maltaisn/game-console/sw/app/system/include/comm.h

/*
 * Copyright 2021 Nicolas Maltais
 *
 * Licensed under the Apache License, Version 2.0 (the "License");
 * you may not use this file except in compliance with the License.
 * You may obtain a copy of the License at
 *
 *     http://www.apache.org/licenses/LICENSE-2.0
 *
 * Unless required by applicable law or agreed to in writing, software
 * distributed under the License is distributed on an "AS IS" BASIS,
 * WITHOUT WARRANTIES OR CONDITIONS OF ANY KIND, either express or implied.
 * See the License for the specific language governing permissions and
 * limitations under the License.
 */

#ifndef SYSTEM_COMM_H
#define SYSTEM_COMM_H

#include <stdint.h>

#define PACKET_SIGNATURE 0x73
#define PACKET_MAX_SIZE 256
#define PACKET_HEADER_SIZE 3
#define PAYLOAD_MAX_SIZE (PACKET_MAX_SIZE - PACKET_HEADER_SIZE)

/*
 * This module defines an interface for communicating to the game console via the UART link.
 * There are a few packets defined for interating with the console.
 * Each packet transmitted and received has the following format:
 *
 * [0]: signature byte 0xc3
 * [1]: packet type
 * [2]: total packet length (=n), -1 (2-255)
 * [3..n]: payload
 *
 * The payload of different packet types defined are described below.
 * "RX" refers to the receiving side of the game console and "TX" refers to the transmitting side.
 *
 * For every packet sent, the transmitter should wait until the response packet is fully received.
 * The reason for this is that the RX buffer size is limited to the size of one packet.
 */

typedef enum {
    /**
     * Get version info
     * - RX payload: empty
     * - TX payload:
     * [0..1]: system app version
     * [2..3]: bootloader version
     * [4..5]: gcprog first compatible version
     */
    PACKET_VERSION = 0x00,

    /**
     * Transfer data on the SPI bus
     * RX & TX packets have an identical format.
     * [0]: bits [0:1] indicate the selected peripheral
     *      - 0x0: flash memory
     *      - 0x1: EEPROM memory
     *      - 0x2: OLED display
     *      - 0x3: reserved
     *      bit [7] is 1 if this is the last transfer, which means the CS line will be
     *      released at the end of transfer. This bit must absolutely be set for the last transfer,
     *      otherwise there might be two CS lines asserted on the next transfer!
     * [1..n]: SPI data
     */
    PACKET_SPI = 0x01,

    /**
     * LOCK: When locked, the system app will be paused and process incoming packets continuously
     * until unlocked. The same packet is used to lock and unlock. This is notably used to do
     * long memory operations split into multiple SPI packets.
     * - RX payload:
     * [0]: 0xff to lock, 0x00 to unlock, others ignored.
     * - TX payload: empty
     */
    PACKET_LOCK = 0x02,

    /**
     * Enable or disable sleep (caused by low power or inactivity).
     * - RX payload:
     * [0]: 0xff to enable sleep, 0x00 to disable, others ignored.
     * - TX payload: empty
     */
    PACKET_SLEEP = 0x03,

    /**
     * Get info on the battery.
     * - RX payload: empty
     * - TX payload:
     * [0]: status (see battery_status_t)
     * [1]: percent (0-100)
     * [2..3]: voltage (in mV)
     * [4..5]: last ADC reading
     */
    PACKET_BATTERY_INFO = 0x10,

    /**
     * Start or stop battery calibration.
     * - RX payload:
     * [0]: 0xff to start, 0x00 to stop, others ignored
     * - TX payload: empty
     */
    PACKET_BATTERY_CALIB = 0x11,

    /**
     * BATTERY_LOAD: if battery calibration is started, set the current "load".
     * - RX payload:
     * [0]: display contrast (0x00-0xff)
     * [1]: display uniform color (disp_color_t)
     * - TX payload: empty
     */
    PACKET_BATTERY_LOAD = 0x12,
} packet_type_t;

/**
 * Receive & decode data from RX.
 * Once a packet signature is detected, this function blocks until packet is fully received.
 * If a fast mode enable packet is received, this function blocks until fast mode is disabled.
 * Must not be called with interrupts enabled.
 */
void comm_receive(void);

#endif //SYSTEM_COMM_H
