maltaisn/game-console/sw/sys/spi.c

/*
 * Copyright 2022 Nicolas Maltais
 *
 * Licensed under the Apache License, Version 2.0 (the "License");
 * you may not use this file except in compliance with the License.
 * You may obtain a copy of the License at
 *
 *     http://www.apache.org/licenses/LICENSE-2.0
 *
 * Unless required by applicable law or agreed to in writing, software
 * distributed under the License is distributed on an "AS IS" BASIS,
 * WITHOUT WARRANTIES OR CONDITIONS OF ANY KIND, either express or implied.
 * See the License for the specific language governing permissions and
 * limitations under the License.
 */

#include <sys/spi.h>
#include <sys/defs.h>

#include <avr/io.h>

#ifdef BOOTLOADER

#include <boot/defs.h>

BOOTLOADER_NOINLINE
void sys_spi_transceive(uint16_t length, uint8_t data[]) {
    // SPI is triple-buffered is the transmit direction and double buffered in the receive direction.
    // Here we only use one buffer level in the transmit direction.
    // 1. Write the first byte to be transmitted.
    // 2. Wait until data register is empty (DREIF=1) and write the second byte to be transmitted.
    // 3. Wait until first byte has been received (RXCIF=1) then read it.
    // 4. Repeat from step 2 until the (n-1) received byte.
    // 5. Wait until last byte has been received (RXCIF=1).
    SPI0.DATA = data[0];
    uint16_t pos = 0;
    while (--length) {
        while (!(SPI0.INTFLAGS & SPI_DREIF_bm));
        SPI0.DATA = data[pos + 1];
        while (!(SPI0.INTFLAGS & SPI_RXCIF_bm));
        data[pos++] = SPI0.DATA;
    }
    while (!(SPI0.INTFLAGS & SPI_RXCIF_bm));
    data[pos] = SPI0.DATA;
}

BOOTLOADER_NOINLINE
void sys_spi_transmit(uint16_t length, const uint8_t data[]) {
    // same as transceive but not receiving.
    SPI0.DATA = *data++;
    while (--length) {
        while (!(SPI0.INTFLAGS & SPI_DREIF_bm));
        SPI0.DATA = *data++;
        while (!(SPI0.INTFLAGS & SPI_RXCIF_bm));
        SPI0.DATA;
    }
    while (!(SPI0.INTFLAGS & SPI_RXCIF_bm));
    SPI0.DATA;
}

BOOTLOADER_NOINLINE
void sys_spi_transmit_single(uint8_t byte) {
    SPI0.DATA = byte;
    while (!(SPI0.INTFLAGS & SPI_RXCIF_bm));
    SPI0.DATA;
}

#endif //BOOTLOADER

ALWAYS_INLINE
void sys_spi_select_flash(void) {
    VPORTF.OUT &= ~PIN0_bm;
}

ALWAYS_INLINE
void sys_spi_select_eeprom(void) {
    VPORTF.OUT &= ~PIN1_bm;
}

ALWAYS_INLINE
void sys_spi_select_display(void) {
    VPORTC.OUT &= ~PIN1_bm;
}

ALWAYS_INLINE
void sys_spi_deselect_flash(void) {
    VPORTF.OUT |= PIN0_bm;
}

ALWAYS_INLINE
void sys_spi_deselect_eeprom(void) {
    VPORTF.OUT |= PIN1_bm;
}

ALWAYS_INLINE
void sys_spi_deselect_display(void) {
    VPORTC.OUT |= PIN1_bm;
}

ALWAYS_INLINE
void sys_spi_deselect_all(void) {
    VPORTF.OUT |= PIN0_bm;
    VPORTF.OUT |= PIN1_bm;
    VPORTC.OUT |= PIN1_bm;
}
