maltaisn/game-console/sw/app/tworld/include/save.h

/*
 * Copyright 2022 Nicolas Maltais
 *
 * Licensed under the Apache License, Version 2.0 (the "License");
 * you may not use this file except in compliance with the License.
 * You may obtain a copy of the License at
 *
 *     http://www.apache.org/licenses/LICENSE-2.0
 *
 * Unless required by applicable law or agreed to in writing, software
 * distributed under the License is distributed on an "AS IS" BASIS,
 * WITHOUT WARRANTIES OR CONDITIONS OF ANY KIND, either express or implied.
 * See the License for the specific language governing permissions and
 * limitations under the License.
 */

#ifndef TWORLD_SAVE_H
#define TWORLD_SAVE_H

#include "game.h"
#include "tworld_level.h"

// Level has never been completed.
#define SAVE_TIME_UNKNOWN 0x3ff
// Level has been completed, but is untimed.
#define SAVE_TIME_UNTIMED 0x3fe

void load_from_eeprom(void);

void save_dialog_options(void);

void update_display_contrast(uint8_t value);

void update_sound_volume(uint8_t volume);

void update_music_enabled(void);

/**
 * Returns the best time for a completed level or `TIME_LEFT_NONE` if not completed.
 * The time is given in number of game ticks left when level is completed,
 * rounded to an in-game second.
 */
time_left_t get_best_level_time(uint16_t pos);

/**
 * For currently loaded level, set best time if time left is better than previous,
 * or if level was not previously completed. Updates data in EEPROM.
 */
void set_best_level_time(void);

/**
 * For `info->total_levels` levels starting at `pos`, set a bit in the completed levels bitset to 1
 * when the level is completed. Sets the number of levels completed and the last unlocked
 * level in the info struct.
 */
void fill_completed_levels_array(uint16_t pos, level_pack_info_t *info);

#endif //TWORLD_SAVE_H
